RGBeter/Sega_32X_MAIN/32X_main1.kicad_sch

## KiCad design 32X_main1.kicad_sch (2026-04-01)

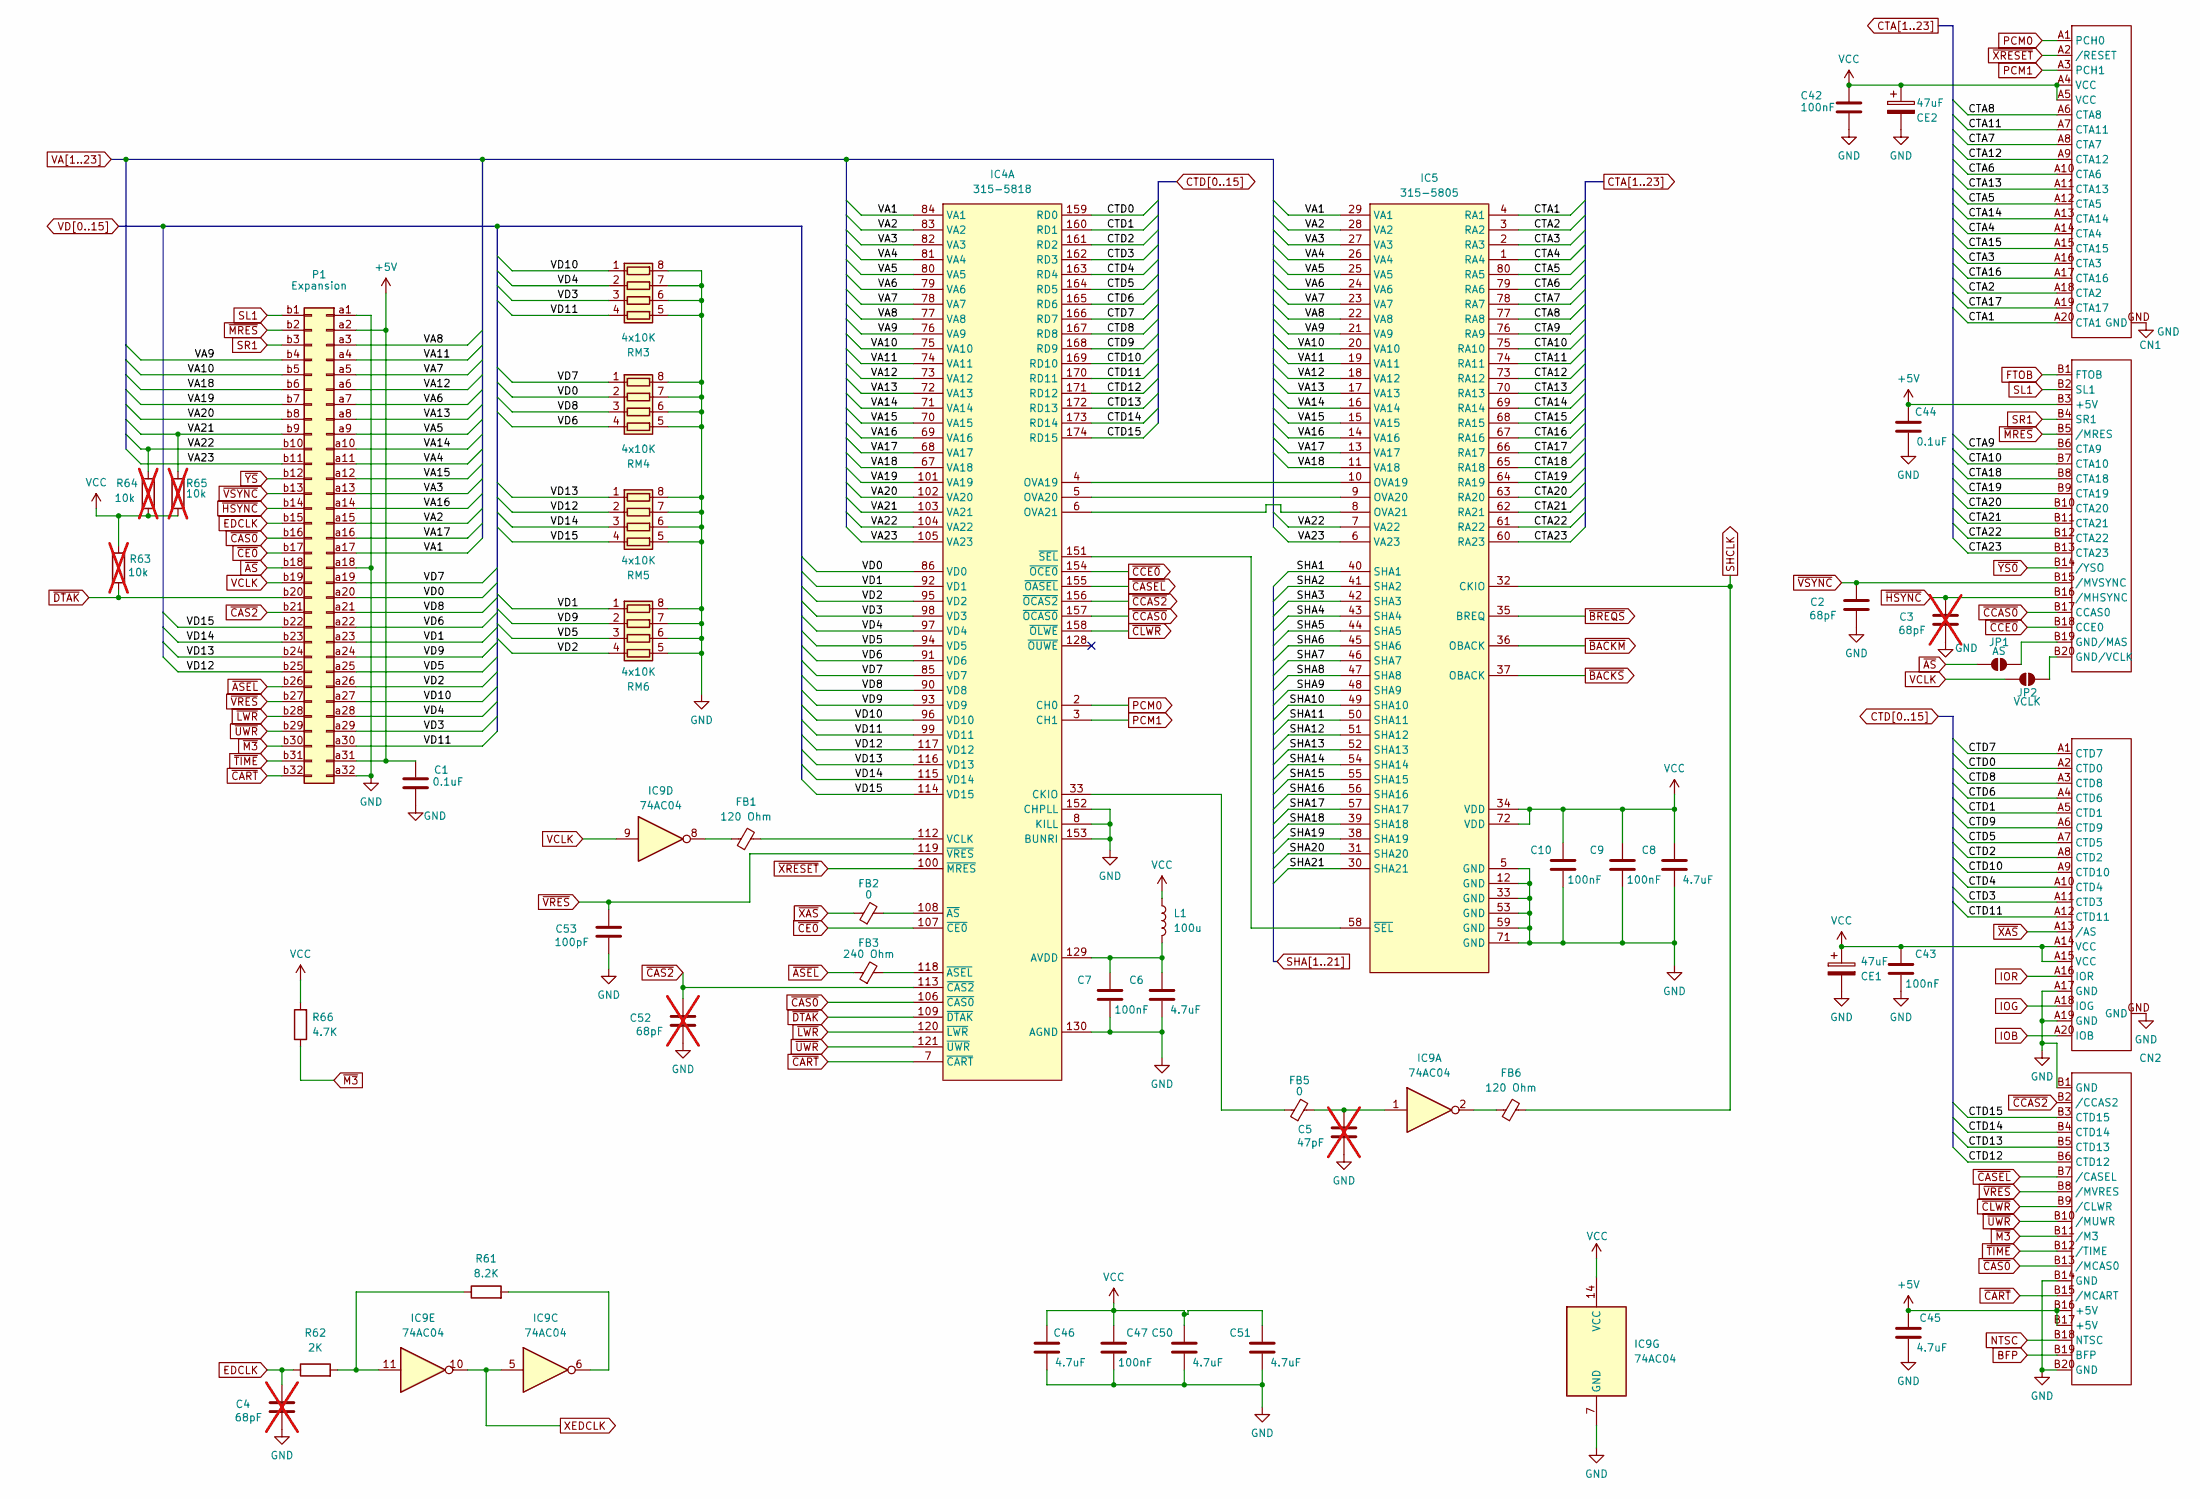
[picture p4: schematic 32X_main1.kicad_sch]

Parts:
C1, C44: 0.1uF; C_0603_1608Metric; MPN VJ1206V475MXJTW1BC; LCSC Part # C132170
C2: 68pF; C_0603_1608Metric; MPN VJ0805A101FXJPW1BC; LCSC Part # C62768
C3, C4, C52: 68pF; C_0603_1608Metric; MPN VJ0805A101FXJPW1BC; LCSC Part # C62768; not fitted
C5: 47pF; C_0603_1608Metric; MPN VJ0805A101FXJPW1BC; LCSC Part # C62768; not fitted
C6, C8, C45, C46, C50, C51: 4.7uF; C_1206_3216Metric; MPN VJ1206V475MXJTW1BC; LCSC Part # C132170
C7, C9, C10, C42, C43, C47: 100nF; C_0603_1608Metric; MPN VJ0805Y104JXJMT; LCSC Part # C111492
C53: 100pF; C_0603_1608Metric; MPN VJ0805A101FXJPW1BC; LCSC Part # C62768
CE1, CE2: 47uF; CP_EIA-6032-28_Kemet-C
CN1, CN2: 32XCN
FB1, FB6: 120 Ohm; L_0603_1608Metric; MPN CBG201209U121T; LCSC Part # C41330
FB2, FB5: 0; L_0603_1608Metric; MPN CBG201209U000T; LCSC Part # C91037
FB3: 240 Ohm; L_0603_1608Metric; MPN CBG201209U221T; LCSC Part # C124102
IC4: 315-5818; LQFP-176_24x24mm_P0.5mm
IC5: 315-5805; PQFP-80_14x20mm_P0.8mm
IC9: 74AC04; SO-14_Dual_Purpose_P1.27mm; MPN SN74AC04DR; LCSC Part # C352940
JP1: AS; SolderJumper-2_P1.3mm_Open_TrianglePad1.0x1.5mm
JP2: VCLK; SolderJumper-2_P1.3mm_Open_TrianglePad1.0x1.5mm
L1: 100u; L_1206_3216Metric; MPN CMI322513J101KT; LCSC Part # C27775
P1: Expansion; Edge-60P
R61: 8.2K; R_0603_1608Metric; MPN CRCW08058K20FKEA; LCSC Part # C844640
R62: 2K; R_0603_1608Metric; MPN CRCW08052K00JNEA; LCSC Part # C2077049
R63, R64, R65: 10k; R_0603_1608Metric; MPN CRCW08052K00JNEA; LCSC Part # C2077049; not fitted
R66: 4.7K; R_0603_1608Metric; MPN CRCW08054K70JNEAC; LCSC Part # C2077067
RM3, RM4, RM5, RM6: 4x10K; R_Array_Convex_4x0603; MPN YC164-FR-0710KL; LCSC Part # C110924

Connections:
+5V: C1.1, C44.1, C45.1, CN1.B3 (+5V), CN2.B16 (+5V), CN2.B17 (+5V), P1.a2, P1.a31 (Pin_a29)
BFP: CN2.B19 (BFP)
CTA1: CN1.A20 (CTA1), IC5.4 (RA1)
CTA2: CN1.A18 (CTA2), IC5.3 (RA2)
CTA3: CN1.A16 (CTA3), IC5.2 (RA3)
CTA4: CN1.A14 (CTA4), IC5.1 (RA4)
CTA5: CN1.A12 (CTA5), IC5.80 (RA5)
CTA6: CN1.A10 (CTA6), IC5.79 (RA6)
CTA7: CN1.A8 (CTA7), IC5.78 (RA7)
CTA8: CN1.A6 (CTA8), IC5.77 (RA8)
CTA9: CN1.B6 (CTA9), IC5.76 (RA9)
CTA10: CN1.B7 (CTA10), IC5.75 (RA10)
CTA11: CN1.A7 (CTA11), IC5.74 (RA11)
CTA12: CN1.A9 (CTA12), IC5.73 (RA12)
CTA13: CN1.A11 (CTA13), IC5.70 (RA13)
CTA14: CN1.A13 (CTA14), IC5.69 (RA14)
CTA15: CN1.A15 (CTA15), IC5.68 (RA15)
CTA16: CN1.A17 (CTA16), IC5.67 (RA16)
CTA17: CN1.A19 (CTA17), IC5.66 (RA17)
CTA18: CN1.B8 (CTA18), IC5.65 (RA18)
CTA19: CN1.B9 (CTA19), IC5.64 (RA19)
CTA20: CN1.B10 (CTA20), IC5.63 (RA20)
CTA21: CN1.B11 (CTA21), IC5.62 (RA21)
CTA22: CN1.B12 (CTA22), IC5.61 (RA22)
CTA23: CN1.B13 (CTA23), IC5.60 (RA23)
CTD0: CN2.A2 (CTD0), IC4.159 (RD0)
CTD1: CN2.A5 (CTD1), IC4.160 (RD1)
CTD2: CN2.A8 (CTD2), IC4.161 (RD2)
CTD3: CN2.A11 (CTD3), IC4.162 (RD3)
CTD4: CN2.A10 (CTD4), IC4.163 (RD4)
CTD5: CN2.A7 (CTD5), IC4.164 (RD5)
CTD6: CN2.A4 (CTD6), IC4.165 (RD6)
CTD7: CN2.A1 (CTD7), IC4.166 (RD7)
CTD8: CN2.A3 (CTD8), IC4.167 (RD8)
CTD9: CN2.A6 (CTD9), IC4.168 (RD9)
CTD10: CN2.A9 (CTD10), IC4.169 (RD10)
CTD11: CN2.A12 (CTD11), IC4.170 (RD11)
CTD12: CN2.B6 (CTD12), IC4.171 (RD12)
CTD13: CN2.B5 (CTD13), IC4.172 (RD13)
CTD14: CN2.B4 (CTD14), IC4.173 (RD14)
CTD15: CN2.B3 (CTD15), IC4.174 (RD15)
EDCLK: C4.1, P1.b15, R62.1
FTOB: CN1.B1 (FTOB)
GND: C1.2, C2.2, C3.2, C4.2, C5.2, C6.2, C7.2, C8.2, C9.2, C10.2, C42.2, C43.2, C44.2, C45.2, C46.2, C47.2, C50.2, C51.2, C52.2, C53.2, CE1.2, CE2.2, CN1.GND, CN2.A17 (GND), CN2.A19 (GND), CN2.B1 (GND), CN2.B14 (GND), CN2.B20 (GND), CN2.GND, IC4.8 (KILL), IC4.130 (AGND), IC4.152 (CHPLL), IC4.153 (BUNRI), IC5.5 (GND), IC5.12 (GND), IC5.33 (GND), IC5.53 (GND), IC5.59 (GND), IC5.71 (GND), IC9.7 (GND), P1.a1, P1.a18, P1.a32 (Pin_a30), RM3.5 (R4.2), RM3.6 (R3.2), RM3.7 (R2.2), RM3.8 (R1.2), RM4.5 (R4.2), RM4.6 (R3.2), RM4.7 (R2.2), RM4.8 (R1.2), RM5.5 (R4.2), RM5.6 (R3.2), RM5.7 (R2.2), RM5.8 (R1.2), RM6.5 (R4.2), RM6.6 (R3.2), RM6.7 (R2.2), RM6.8 (R1.2)
IOB: CN2.A20 (IOB)
IOG: CN2.A18 (IOG)
IOR: CN2.A16 (IOR)
NTSC: CN2.B18 (NTSC)
unnamed: C5.1, FB5.2, IC9.1
unnamed: C6.1, C7.1, IC4.129 (AVDD), L1.2
unnamed: CN1.B19 (GND/MAS), JP1.2 (B)
unnamed: CN1.B20 (GND/VCLK), JP2.2 (B)
unnamed: FB1.1, IC9.8
unnamed: FB1.2, IC4.112 (VCLK)
unnamed: FB2.2, IC4.108 (~AS)
unnamed: FB3.2, IC4.118 (~ASEL)
unnamed: FB5.1, IC4.33 (CKIO)
unnamed: FB6.1, IC9.2
unnamed: IC4.4 (OVA19), IC5.10 (OVA19)
unnamed: IC4.5 (OVA20), IC5.9 (OVA20)
unnamed: IC4.6 (OVA21), IC5.8 (OVA21)
unnamed: IC4.151 (~SEL), IC5.58 (~SEL)
unnamed: IC9.6, R61.2
unnamed: IC9.11, R61.1, R62.2
PCM0: CN1.A1 (PCH0), IC4.2 (CH0)
PCM1: CN1.A3 (PCH1), IC4.3 (CH1)
SHA1: IC5.40 (SHA1)
SHA2: IC5.41 (SHA2)
SHA3: IC5.42 (SHA3)
SHA4: IC5.43 (SHA4)
SHA5: IC5.44 (SHA5)
SHA6: IC5.45 (SHA6)
SHA7: IC5.46 (SHA7)
SHA8: IC5.47 (SHA8)
SHA9: IC5.48 (SHA9)
SHA10: IC5.49 (SHA10)
SHA11: IC5.50 (SHA11)
SHA12: IC5.51 (SHA12)
SHA13: IC5.52 (SHA13)
SHA14: IC5.54 (SHA14)
SHA15: IC5.55 (SHA15)
SHA16: IC5.56 (SHA16)
SHA17: IC5.57 (SHA17)
SHA18: IC5.39 (SHA18)
SHA19: IC5.38 (SHA19)
SHA20: IC5.31 (SHA20)
SHA21: IC5.30 (SHA21)
SHCLK: FB6.2, IC5.32 (CKIO)
SL1: CN1.B2 (SL1), P1.b1
SR1: CN1.B4 (SR1), P1.b3
VA1: IC4.84 (VA1), IC5.29 (VA1), P1.a17
VA2: IC4.83 (VA2), IC5.28 (VA2), P1.a15
VA3: IC4.82 (VA3), IC5.27 (VA3), P1.a13
VA4: IC4.81 (VA4), IC5.26 (VA4), P1.a11
VA5: IC4.80 (VA5), IC5.25 (VA5), P1.a9
VA6: IC4.79 (VA6), IC5.24 (VA6), P1.a7
VA7: IC4.78 (VA7), IC5.23 (VA7), P1.a5
VA8: IC4.77 (VA8), IC5.22 (VA8), P1.a3
VA9: IC4.76 (VA9), IC5.21 (VA9), P1.b4
VA10: IC4.75 (VA10), IC5.20 (VA10), P1.b5
VA11: IC4.74 (VA11), IC5.19 (VA11), P1.a4
VA12: IC4.73 (VA12), IC5.18 (VA12), P1.a6
VA13: IC4.72 (VA13), IC5.17 (VA13), P1.a8
VA14: IC4.71 (VA14), IC5.16 (VA14), P1.a10
VA15: IC4.70 (VA15), IC5.15 (VA15), P1.a12
VA16: IC4.69 (VA16), IC5.14 (VA16), P1.a14
VA17: IC4.68 (VA17), IC5.13 (VA17), P1.a16
VA18: IC4.67 (VA18), IC5.11 (VA18), P1.b6
VA19: IC4.101 (VA19), P1.b7
VA20: IC4.102 (VA20), P1.b8
VA21: IC4.103 (VA21), P1.b9, R65.2
VA22: IC4.104 (VA22), IC5.7 (VA22), P1.b10, R64.2
VA23: IC4.105 (VA23), IC5.6 (VA23), P1.b11
VCC: C8.1, C9.1, C10.1, C42.1, C43.1, C46.1, C47.1, C50.1, C51.1, CE1.1, CE2.1, CN1.A4 (VCC), CN1.A5 (VCC), CN2.A14 (VCC), CN2.A15 (VCC), IC5.34 (VDD), IC5.72 (VDD), IC9.14 (VCC), L1.1, R63.2, R64.1, R65.1, R66.2
VCLK: IC9.9, JP2.1 (A), P1.b19
VD0: IC4.86 (VD0), P1.a20, RM4.2 (R2.1)
VD1: IC4.92 (VD1), P1.a23, RM6.1 (R1.1)
VD2: IC4.95 (VD2), P1.a26, RM6.4 (R4.1)
VD3: IC4.98 (VD3), P1.a29, RM3.3 (R3.1)
VD4: IC4.97 (VD4), P1.a28, RM3.2 (R2.1)
VD5: IC4.94 (VD5), P1.a25, RM6.3 (R3.1)
VD6: IC4.91 (VD6), P1.a22, RM4.4 (R4.1)
VD7: IC4.85 (VD7), P1.a19, RM4.1 (R1.1)
VD8: IC4.90 (VD8), P1.a21, RM4.3 (R3.1)
VD9: IC4.93 (VD9), P1.a24, RM6.2 (R2.1)
VD10: IC4.96 (VD10), P1.a27, RM3.1 (R1.1)
VD11: IC4.99 (VD11), P1.a30, RM3.4 (R4.1)
VD12: IC4.117 (VD12), P1.b25, RM5.2 (R2.1)
VD13: IC4.116 (VD13), P1.b24, RM5.1 (R1.1)
VD14: IC4.115 (VD14), P1.b23, RM5.3 (R3.1)
VD15: IC4.114 (VD15), P1.b22, RM5.4 (R4.1)
XEDCLK: IC9.5, IC9.10
~ASEL: FB3.1, P1.b26
~AS: JP1.1 (A), P1.b18
~BACKM: IC5.36 (OBACK)
~BACKS: IC5.37 (OBACK)
~BREQS: IC5.35 (BREQ)
~CART: CN2.B15 (/MCART), IC4.7 (~CART), P1.b32 (Pin_b30)
~CAS0: CN2.B13 (/MCAS0), IC4.106 (~CAS0), P1.b16
~CAS2: C52.1, IC4.113 (~CAS2), P1.b21
~CASEL: CN2.B7 (/CASEL), IC4.155 (~OASEL)
~CCAS0: CN1.B17 (CCAS0), IC4.157 (~OCAS0)
~CCAS2: CN2.B2 (/CCAS2), IC4.156 (~OCAS2)
~CCE0: CN1.B18 (CCE0), IC4.154 (~OCE0)
~CE0: IC4.107 (~CE0), P1.b17
~CLWR: CN2.B9 (/CLWR), IC4.158 (~OLWE)
~DTAK: IC4.109 (~DTAK), P1.b20, R63.1
~HSYNC: C3.1, CN1.B16 (/MHSYNC), P1.b14
~LWR: IC4.120 (~LWR), P1.b28
~M3: CN2.B11 (/M3), P1.b30, R66.1
~MRES: CN1.B5 (/MRES), P1.b2
~TIME: CN2.B12 (/TIME), P1.b31 (Pin_b29)
~UWR: CN2.B10 (/MUWR), IC4.121 (~UWR), P1.b29
~VRES: C53.1, CN2.B8 (/MVRES), IC4.119 (~VRES), P1.b27
~VSYNC: C2.1, CN1.B15 (/MVSYNC), P1.b13
~XAS: CN2.A13 (/AS), FB2.1
~XRESET: CN1.A2 (/RESET), IC4.100 (~MRES)
~YS0: CN1.B14 (/YSO)
~YS: P1.b12
