RGBeter/Sega_32X_MAIN/32X_main2.kicad_sch

## KiCad design 32X_main2.kicad_sch (2026-04-01)

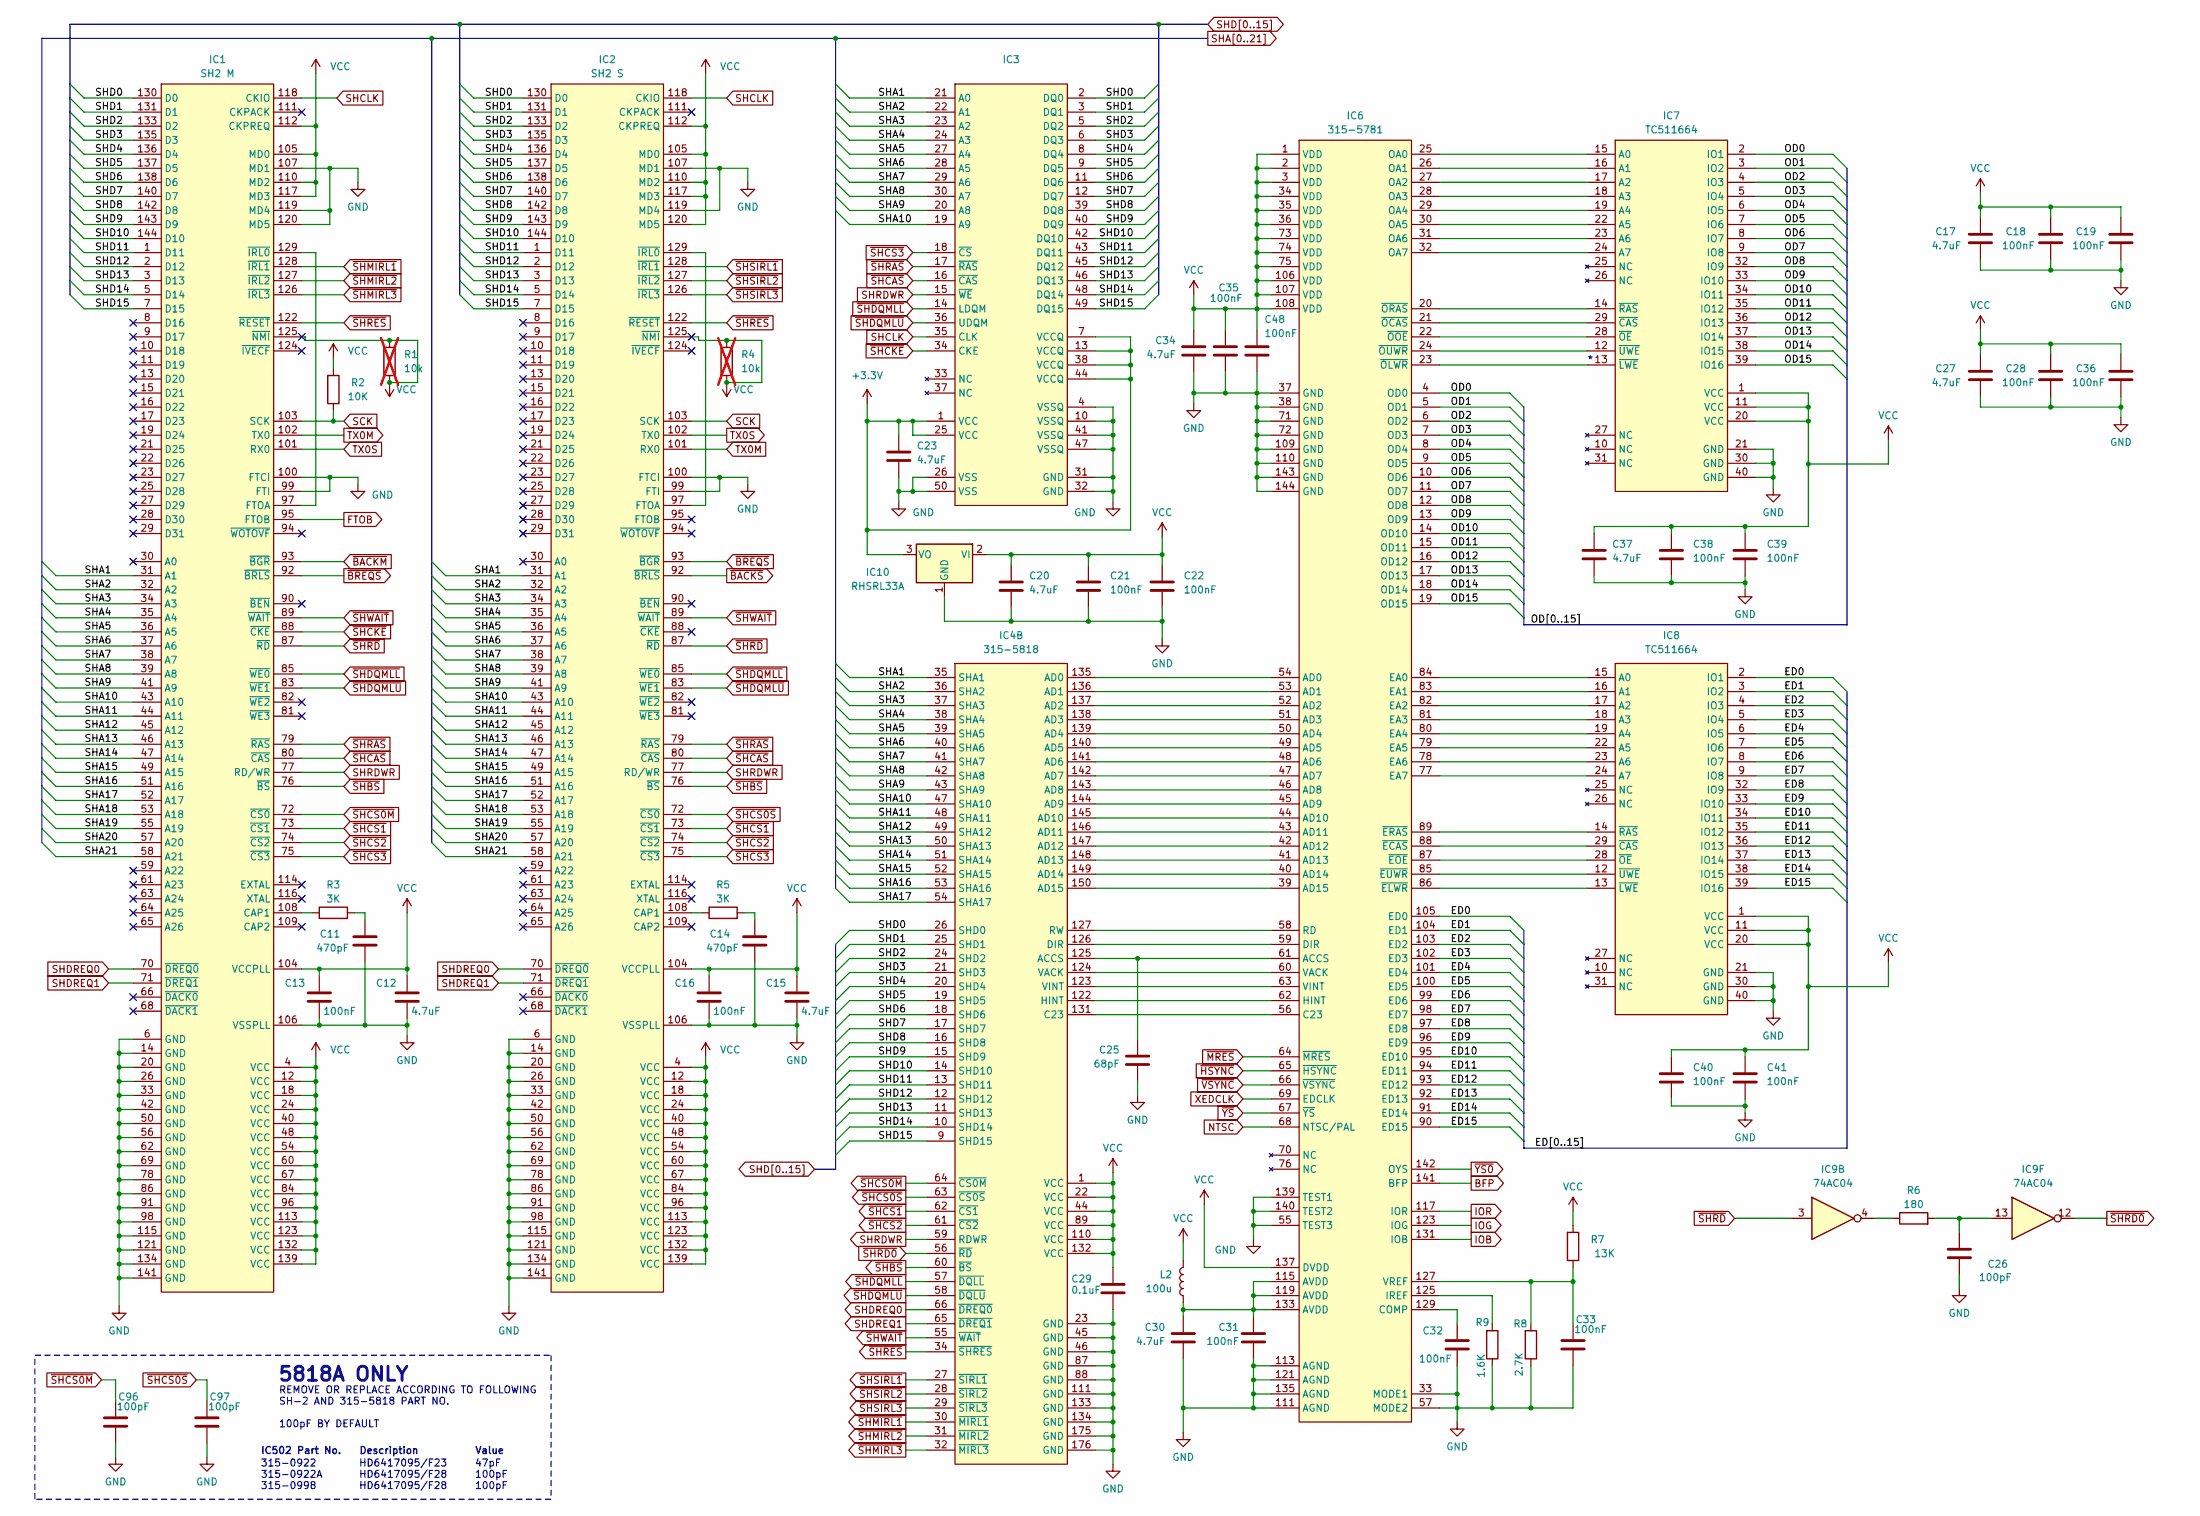
[picture p5: schematic 32X_main2.kicad_sch]

Parts:
C11, C14: 470pF; C_0603_1608Metric; MPN VJ0805A471FXJPW1BC; LCSC Part # C62771
C12, C15, C17, C20, C23, C27, C30, C34, C37: 4.7uF; C_1206_3216Metric; MPN VJ1206V475MXJTW1BC; LCSC Part # C132170
C13, C16, C18, C19, C21, C22, C28, C31, C32, C33, C35, C36, C38, C39, C40, C41, C48: 100nF; C_0603_1608Metric; MPN VJ0805Y104JXJMT; LCSC Part # C111492
C25: 68pF; C_0603_1608Metric; MPN GRM21A5C2J680JWA1D; LCSC Part # C162306
C26: 100pF; C_0603_1608Metric; MPN VJ0805A101FXJPW1BC; LCSC Part # C62768
C29: 0.1uF; C_0603_1608Metric; MPN VJ1206V475MXJTW1BC; LCSC Part # C132170
C96, C97: 100pF; C_0603_1608Metric; MPN VJ0805Y104JXJMT; LCSC Part # C111492
IC1: SH2 M; LQFP-144_20x20mm_P0.5mm
IC2: SH2 S; LQFP-144_20x20mm_P0.5mm
IC3: µPD4502161; SSOP-50
IC4: 315-5818; LQFP-176_24x24mm_P0.5mm
IC6: 315-5781; LQFP-144_20x20mm_P0.5mm
IC7, IC8: TC511664; SO-Mix-40
IC9: 74AC04; SO-14_Dual_Purpose_P1.27mm; MPN SN74AC04DR; LCSC Part # C352940
IC10: RHSRL33A; SOT-89-3_Handsoldering
L2: 100u; L_1206_3216Metric; MPN CMI322513J101KT; LCSC Part # C27775
R1, R4: 10k; R_0603_1608Metric; MPN CRCW08052K00JNEA; LCSC Part # C2077049; not fitted
R2: 10K; R_0603_1608Metric; MPN CRCW080510K0FKEA; LCSC Part # C844937
R3, R5: 3K; R_0603_1608Metric; MPN CRCW08053K00FKEA; LCSC Part # C114222
R6: 180; R_0603_1608Metric; MPN CRCW0805180RJNEA; LCSC Part # C137585
R7: 13K; R_0603_1608Metric; MPN CRCW080513K0FKEA; LCSC Part # C844395
R8: 2.7K; R_0603_1608Metric; MPN CRCW08052K70FKEA; LCSC Part # C844836
R9: 1.6K; R_0603_1608Metric; MPN CRCW08051K60FKEA; LCSC Part # C185279

Connections:
+3.3V: C23.1, IC3.1 (VCC), IC3.7 (VCCQ), IC3.13 (VCCQ), IC3.25 (VCC), IC3.38 (VCCQ), IC3.44 (VCCQ), IC10.3 (VO)
BFP: IC6.141 (BFP)
ED0: IC6.105 (ED0), IC8.2 (IO1)
ED1: IC6.104 (ED1), IC8.3 (IO2)
ED2: IC6.103 (ED2), IC8.4 (IO3)
ED3: IC6.102 (ED3), IC8.5 (IO4)
ED4: IC6.101 (ED4), IC8.6 (IO5)
ED5: IC6.100 (ED5), IC8.7 (IO6)
ED6: IC6.99 (ED6), IC8.8 (IO7)
ED7: IC6.98 (ED7), IC8.9 (IO8)
ED8: IC6.97 (ED8), IC8.32 (IO9)
ED9: IC6.96 (ED9), IC8.33 (IO10)
ED10: IC6.95 (ED10), IC8.34 (IO11)
ED11: IC6.94 (ED11), IC8.35 (IO12)
ED12: IC6.93 (ED12), IC8.36 (IO13)
ED13: IC6.92 (ED13), IC8.37 (IO14)
ED14: IC6.91 (ED14), IC8.38 (IO15)
ED15: IC6.90 (ED15), IC8.39 (IO16)
FTOB: IC1.95 (FTOB)
GND: C11.2, C12.2, C13.2, C14.2, C15.2, C16.2, C17.2, C18.2, C19.2, C20.2, C21.2, C22.2, C23.2, C25.2, C26.2, C27.2, C28.2, C29.2, C30.2, C31.2, C32.2, C33.2, C34.2, C35.2, C36.2, C37.2, C38.2, C39.2, C40.2, C41.2, C48.2, C96.2, C97.2, IC1.6 (GND), IC1.14 (GND), IC1.20 (GND), IC1.26 (GND), IC1.33 (GND), IC1.42 (GND), IC1.50 (GND), IC1.56 (GND), IC1.62 (GND), IC1.69 (GND), IC1.78 (GND), IC1.86 (GND), IC1.91 (GND), IC1.98 (GND), IC1.99 (FTI), IC1.100 (FTCI), IC1.106 (VSSPLL), IC1.107 (MD1), IC1.115 (GND), IC1.119 (MD4), IC1.120 (MD5), IC1.121 (GND), IC1.134 (GND), IC1.141 (GND), IC2.6 (GND), IC2.14 (GND), IC2.20 (GND), IC2.26 (GND), IC2.33 (GND), IC2.42 (GND), IC2.50 (GND), IC2.56 (GND), IC2.62 (GND), IC2.69 (GND), IC2.78 (GND), IC2.86 (GND), IC2.91 (GND), IC2.98 (GND), IC2.99 (FTI), IC2.100 (FTCI), IC2.106 (VSSPLL), IC2.107 (MD1), IC2.115 (GND), IC2.119 (MD4), IC2.121 (GND), IC2.134 (GND), IC2.141 (GND), IC3.4 (VSSQ), IC3.10 (VSSQ), IC3.26 (VSS), IC3.31 (GND), IC3.32 (GND), IC3.41 (VSSQ), IC3.47 (VSSQ), IC3.50 (VSS), IC4.23 (GND), IC4.45 (GND), IC4.46 (GND), IC4.87 (GND), IC4.88 (GND), IC4.111 (GND), IC4.133 (GND), IC4.134 (GND), IC4.175 (GND), IC4.176 (GND), IC6.33 (MODE1), IC6.37 (GND), IC6.38 (GND), IC6.55 (TEST3), IC6.57 (MODE2), IC6.71 (GND), IC6.72 (GND), IC6.109 (GND), IC6.110 (GND), IC6.111 (AGND), IC6.113 (AGND), IC6.121 (AGND), IC6.135 (AGND), IC6.139 (TEST1), IC6.140 (TEST2), IC6.143 (GND), IC6.144 (GND), IC7.21 (GND), IC7.30 (GND), IC7.40 (GND), IC8.21 (GND), IC8.30 (GND), IC8.40 (GND), IC10.1 (GND), R8.1, R9.1
IOB: IC6.131 (IOB)
IOG: IC6.123 (IOG)
IOR: IC6.117 (IOR)
NTSC: IC6.68 (NTSC/PAL)
unnamed: C11.1, R3.2
unnamed: C14.1, R5.2
unnamed: C25.1, IC4.125 (ACCS), IC6.61 (ACCS)
unnamed: C26.1, IC9.13, R6.2
unnamed: C30.1, C31.1, IC6.115 (AVDD), IC6.119 (AVDD), IC6.133 (AVDD), L2.2
unnamed: C32.1, IC6.129 (COMP)
unnamed: C33.1, IC6.127 (VREF), R7.1, R8.2
unnamed: IC1.108 (CAP1), R3.1
unnamed: IC1.97 (FTOA), IC1.129 (~IRL0)
unnamed: IC2.108 (CAP1), R5.1
unnamed: IC2.97 (FTOA), IC2.129 (~IRL0)
unnamed: IC4.122 (HINT), IC6.62 (HINT)
unnamed: IC4.123 (VINT), IC6.63 (VINT)
unnamed: IC4.124 (VACK), IC6.60 (VACK)
unnamed: IC4.126 (DIR), IC6.59 (DIR)
unnamed: IC4.127 (RW), IC6.58 (RD)
unnamed: IC4.131 (C23), IC6.56 (C23)
unnamed: IC4.135 (AD0), IC6.54 (AD0)
unnamed: IC4.136 (AD1), IC6.53 (AD1)
unnamed: IC4.137 (AD2), IC6.52 (AD2)
unnamed: IC4.138 (AD3), IC6.51 (AD3)
unnamed: IC4.139 (AD4), IC6.50 (AD4)
unnamed: IC4.140 (AD5), IC6.49 (AD5)
unnamed: IC4.141 (AD6), IC6.48 (AD6)
unnamed: IC4.142 (AD7), IC6.47 (AD7)
unnamed: IC4.143 (AD8), IC6.46 (AD8)
unnamed: IC4.144 (AD9), IC6.45 (AD9)
unnamed: IC4.145 (AD10), IC6.44 (AD10)
unnamed: IC4.146 (AD11), IC6.43 (AD11)
unnamed: IC4.147 (AD12), IC6.42 (AD12)
unnamed: IC4.148 (AD13), IC6.41 (AD13)
unnamed: IC4.149 (AD14), IC6.40 (AD14)
unnamed: IC4.150 (AD15), IC6.39 (AD15)
unnamed: IC6.20 (~ORAS), IC7.14 (~RAS)
unnamed: IC6.21 (~OCAS), IC7.29 (~CAS)
unnamed: IC6.22 (~OOE), IC7.28 (~OE)
unnamed: IC6.23 (~OLWR), IC7.13 (~LWE)
unnamed: IC6.24 (~OUWR), IC7.12 (~UWE)
unnamed: IC6.25 (OA0), IC7.15 (A0)
unnamed: IC6.26 (OA1), IC7.16 (A1)
unnamed: IC6.27 (OA2), IC7.17 (A2)
unnamed: IC6.28 (OA3), IC7.18 (A3)
unnamed: IC6.29 (OA4), IC7.19 (A4)
unnamed: IC6.30 (OA5), IC7.22 (A5)
unnamed: IC6.31 (OA6), IC7.23 (A6)
unnamed: IC6.32 (OA7), IC7.24 (A7)
unnamed: IC6.77 (EA7), IC8.24 (A7)
unnamed: IC6.78 (EA6), IC8.23 (A6)
unnamed: IC6.79 (EA5), IC8.22 (A5)
unnamed: IC6.80 (EA4), IC8.19 (A4)
unnamed: IC6.81 (EA3), IC8.18 (A3)
unnamed: IC6.82 (EA2), IC8.17 (A2)
unnamed: IC6.83 (EA1), IC8.16 (A1)
unnamed: IC6.84 (EA0), IC8.15 (A0)
unnamed: IC6.85 (~EUWR), IC8.12 (~UWE)
unnamed: IC6.86 (~ELWR), IC8.13 (~LWE)
unnamed: IC6.87 (~EOE), IC8.28 (~OE)
unnamed: IC6.88 (~ECAS), IC8.29 (~CAS)
unnamed: IC6.89 (~ERAS), IC8.14 (~RAS)
unnamed: IC6.125 (IREF), R9.2
unnamed: IC9.4, R6.1
OD0: IC6.4 (OD0), IC7.2 (IO1)
OD1: IC6.5 (OD1), IC7.3 (IO2)
OD2: IC6.6 (OD2), IC7.4 (IO3)
OD3: IC6.7 (OD3), IC7.5 (IO4)
OD4: IC6.8 (OD4), IC7.6 (IO5)
OD5: IC6.9 (OD5), IC7.7 (IO6)
OD6: IC6.10 (OD6), IC7.8 (IO7)
OD7: IC6.11 (OD7), IC7.9 (IO8)
OD8: IC6.12 (OD8), IC7.32 (IO9)
OD9: IC6.13 (OD9), IC7.33 (IO10)
OD10: IC6.14 (OD10), IC7.34 (IO11)
OD11: IC6.15 (OD11), IC7.35 (IO12)
OD12: IC6.16 (OD12), IC7.36 (IO13)
OD13: IC6.17 (OD13), IC7.37 (IO14)
OD14: IC6.18 (OD14), IC7.38 (IO15)
OD15: IC6.19 (OD15), IC7.39 (IO16)
SCK: IC1.103 (SCK), IC2.103 (SCK), R2.1
SHA1: IC1.31 (A1), IC2.31 (A1), IC3.21 (A0), IC4.35 (SHA1)
SHA2: IC1.32 (A2), IC2.32 (A2), IC3.22 (A1), IC4.36 (SHA2)
SHA3: IC1.34 (A3), IC2.34 (A3), IC3.23 (A2), IC4.37 (SHA3)
SHA4: IC1.35 (A4), IC2.35 (A4), IC3.24 (A3), IC4.38 (SHA4)
SHA5: IC1.36 (A5), IC2.36 (A5), IC3.27 (A4), IC4.39 (SHA5)
SHA6: IC1.37 (A6), IC2.37 (A6), IC3.28 (A5), IC4.40 (SHA6)
SHA7: IC1.38 (A7), IC2.38 (A7), IC3.29 (A6), IC4.41 (SHA7)
SHA8: IC1.39 (A8), IC2.39 (A8), IC3.30 (A7), IC4.42 (SHA8)
SHA9: IC1.41 (A9), IC2.41 (A9), IC3.20 (A8), IC4.43 (SHA9)
SHA10: IC1.43 (A10), IC2.43 (A10), IC3.19 (A9), IC4.47 (SHA10)
SHA11: IC1.44 (A11), IC2.44 (A11), IC4.48 (SHA11)
SHA12: IC1.45 (A12), IC2.45 (A12), IC4.49 (SHA12)
SHA13: IC1.46 (A13), IC2.46 (A13), IC4.50 (SHA13)
SHA14: IC1.47 (A14), IC2.47 (A14), IC4.51 (SHA14)
SHA15: IC1.49 (A15), IC2.49 (A15), IC4.52 (SHA15)
SHA16: IC1.51 (A16), IC2.51 (A16), IC4.53 (SHA16)
SHA17: IC1.52 (A17), IC2.52 (A17), IC4.54 (SHA17)
SHA18: IC1.53 (A18), IC2.53 (A18)
SHA19: IC1.55 (A19), IC2.55 (A19)
SHA20: IC1.57 (A20), IC2.57 (A20)
SHA21: IC1.58 (A21), IC2.58 (A21)
SHCLK: IC1.118 (CKIO), IC2.118 (CKIO), IC3.35 (CLK)
SHD0: IC1.130 (D0), IC2.130 (D0), IC3.2 (DQ0), IC4.26 (SHD0)
SHD1: IC1.131 (D1), IC2.131 (D1), IC3.3 (DQ1), IC4.25 (SHD1)
SHD2: IC1.133 (D2), IC2.133 (D2), IC3.5 (DQ2), IC4.24 (SHD2)
SHD3: IC1.135 (D3), IC2.135 (D3), IC3.6 (DQ3), IC4.21 (SHD3)
SHD4: IC1.136 (D4), IC2.136 (D4), IC3.8 (DQ4), IC4.20 (SHD4)
SHD5: IC1.137 (D5), IC2.137 (D5), IC3.9 (DQ5), IC4.19 (SHD5)
SHD6: IC1.138 (D6), IC2.138 (D6), IC3.11 (DQ6), IC4.18 (SHD6)
SHD7: IC1.140 (D7), IC2.140 (D7), IC3.12 (DQ7), IC4.17 (SHD7)
SHD8: IC1.142 (D8), IC2.142 (D8), IC3.39 (DQ8), IC4.16 (SHD8)
SHD9: IC1.143 (D9), IC2.143 (D9), IC3.40 (DQ9), IC4.15 (SHD9)
SHD10: IC1.144 (D10), IC2.144 (D10), IC3.42 (DQ10), IC4.14 (SHD10)
SHD11: IC1.1 (D11), IC2.1 (D11), IC3.43 (DQ11), IC4.13 (SHD11)
SHD12: IC1.2 (D12), IC2.2 (D12), IC3.45 (DQ12), IC4.12 (SHD12)
SHD13: IC1.3 (D13), IC2.3 (D13), IC3.46 (DQ13), IC4.11 (SHD13)
SHD14: IC1.5 (D14), IC2.5 (D14), IC3.48 (DQ14), IC4.10 (SHD14)
SHD15: IC1.7 (D15), IC2.7 (D15), IC3.49 (DQ15), IC4.9 (SHD15)
SHDREQ0: IC1.70 (~DREQ0), IC2.70 (~DREQ0), IC4.66 (~DREQ0)
SHDREQ1: IC1.71 (~DREQ1), IC2.71 (~DREQ1), IC4.65 (~DREQ1)
SHRDWR: IC1.77 (RD/WR), IC2.77 (RD/WR), IC3.15 (~WE), IC4.59 (RDWR)
TX0M: IC1.102 (TX0), IC2.101 (RX0)
TX0S: IC1.101 (RX0), IC2.102 (TX0)
VCC: C12.1, C13.1, C15.1, C16.1, C17.1, C18.1, C19.1, C20.1, C21.1, C22.1, C27.1, C28.1, C29.1, C34.1, C35.1, C36.1, C37.1, C38.1, C39.1, C40.1, C41.1, C48.1, IC1.4 (VCC), IC1.12 (VCC), IC1.18 (VCC), IC1.24 (VCC), IC1.40 (VCC), IC1.48 (VCC), IC1.54 (VCC), IC1.60 (VCC), IC1.67 (VCC), IC1.84 (VCC), IC1.96 (VCC), IC1.104 (VCCPLL), IC1.105 (MD0), IC1.110 (MD2), IC1.112 (CKPREQ), IC1.113 (VCC), IC1.117 (MD3), IC1.123 (VCC), IC1.125 (~NMI), IC1.132 (VCC), IC1.139 (VCC), IC2.4 (VCC), IC2.12 (VCC), IC2.18 (VCC), IC2.24 (VCC), IC2.40 (VCC), IC2.48 (VCC), IC2.54 (VCC), IC2.60 (VCC), IC2.67 (VCC), IC2.84 (VCC), IC2.96 (VCC), IC2.104 (VCCPLL), IC2.105 (MD0), IC2.110 (MD2), IC2.112 (CKPREQ), IC2.113 (VCC), IC2.117 (MD3), IC2.120 (MD5), IC2.123 (VCC), IC2.125 (~NMI), IC2.132 (VCC), IC2.139 (VCC), IC4.1 (VCC), IC4.22 (VCC), IC4.44 (VCC), IC4.89 (VCC), IC4.110 (VCC), IC4.132 (VCC), IC6.1 (VDD), IC6.2 (VDD), IC6.3 (VDD), IC6.34 (VDD), IC6.35 (VDD), IC6.36 (VDD), IC6.73 (VDD), IC6.74 (VDD), IC6.75 (VDD), IC6.106 (VDD), IC6.107 (VDD), IC6.108 (VDD), IC6.137 (DVDD), IC7.1 (VCC), IC7.11 (VCC), IC7.20 (VCC), IC8.1 (VCC), IC8.11 (VCC), IC8.20 (VCC), IC10.2 (VI), L2.1, R1.1, R1.2, R2.2, R4.1, R4.2, R7.2
XEDCLK: IC6.69 (EDCLK)
~BACKM: IC1.93 (~BGR)
~BACKS: IC2.92 (~BRLS)
~BREQS: IC1.92 (~BRLS), IC2.93 (~BGR)
~HSYNC: IC6.65 (~HSYNC)
~MRES: IC6.64 (~MRES)
~SHBS: IC1.76 (~BS), IC2.76 (~BS), IC4.60 (~BS)
~SHCAS: IC1.80 (~CAS), IC2.80 (~CAS), IC3.16 (~CAS)
~SHCKE: IC1.88 (~CKE), IC3.34 (CKE)
~SHCS0M: C96.1, IC1.72 (~CS0), IC4.64 (~CS0M)
~SHCS0S: C97.1, IC2.72 (~CS0), IC4.63 (~CS0S)
~SHCS1: IC1.73 (~CS1), IC2.73 (~CS1), IC4.62 (~CS1)
~SHCS2: IC1.74 (~CS2), IC2.74 (~CS2), IC4.61 (~CS2)
~SHCS3: IC1.75 (~CS3), IC2.75 (~CS3), IC3.18 (~CS)
~SHDQMLL: IC1.85 (~WE0), IC2.85 (~WE0), IC3.14 (LDQM), IC4.57 (~DQLL)
~SHDQMLU: IC1.83 (~WE1), IC2.83 (~WE1), IC3.36 (UDQM), IC4.58 (~DQLU)
~SHMIRL1: IC1.128 (~IRL1), IC4.30 (~MIRL1)
~SHMIRL2: IC1.127 (~IRL2), IC4.31 (~MIRL2)
~SHMIRL3: IC1.126 (~IRL3), IC4.32 (~MIRL3)
~SHRAS: IC1.79 (~RAS), IC2.79 (~RAS), IC3.17 (~RAS)
~SHRD0: IC4.56 (~RD), IC9.12
~SHRD: IC1.87 (~RD), IC2.87 (~RD), IC9.3
~SHRES: IC1.122 (~RESET), IC2.122 (~RESET), IC4.34 (~SHRES)
~SHSIRL1: IC2.128 (~IRL1), IC4.27 (~SIRL1)
~SHSIRL2: IC2.127 (~IRL2), IC4.28 (~SIRL2)
~SHSIRL3: IC2.126 (~IRL3), IC4.29 (~SIRL3)
~SHWAIT: IC1.89 (~WAIT), IC2.89 (~WAIT), IC4.55 (~WAIT)
~VSYNC: IC6.66 (~VSYNC)
~YS0: IC6.142 (OYS)
~YS: IC6.67 (~YS)

Notes on the sheet:
315-0922 315-0922A 315-0998
5818A ONLY
REMOVE OR REPLACE ACCORDING TO FOLLOWING SH-2 AND 315-5818 PART NO. 100pF BY DEFAULT
IC502 Part No.
Value
Description
47pF 100pF 100pF
HD6417095/F23 HD6417095/F28 HD6417095/F28
